GeorgeChiou/ESP32-CAM-MotorShield-V3.0-TANKGO/3DP STL TANKGO/截圖 2022-04-06 下午12.41.42.png

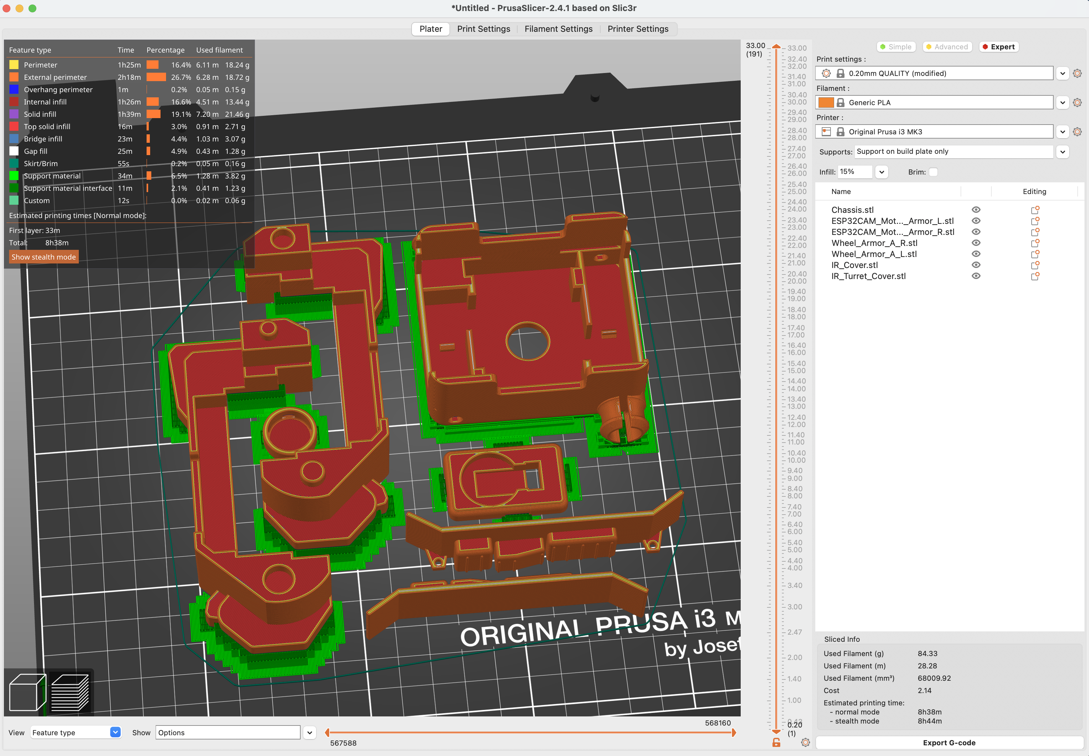
3DP STL TANKGO/截圖 2022-04-06 下午12.41.42.png
