GeorgeChiou/ESP32-CAM-MotorShield-V3.0-TANKGO/Pictures/IMG_5468.JPG

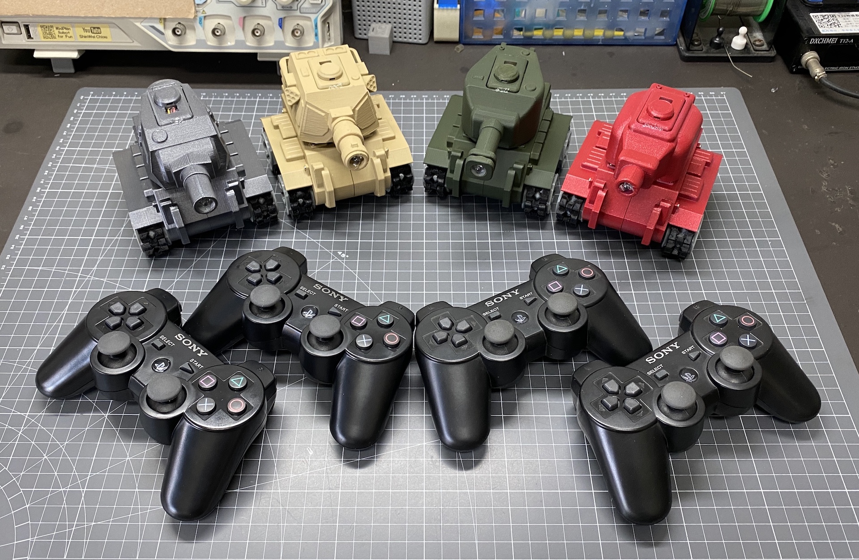
Pictures/IMG_5468.JPG
