GeorgeChiou/ESP32-CAM-MotorShield-V3.0-TANKGO/Program/Arduion IDE set.png

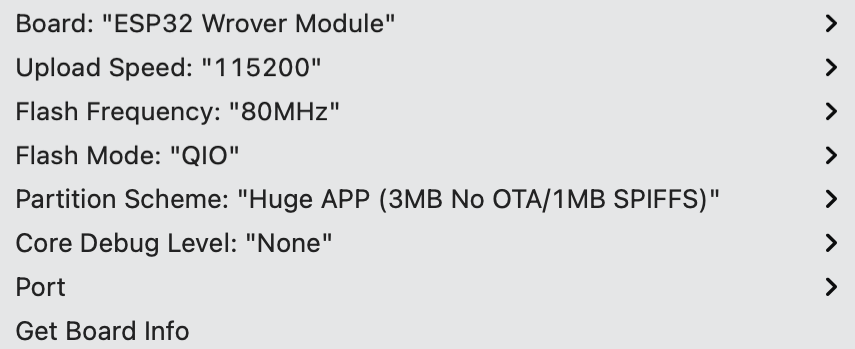
Program/Arduion IDE set.png
