GeorgeChiou/ESP32-CAM-MotorShield-V3.0-TANKGO/Assembly Instruction/ESP32-CAM Motor Shield V3.0  - Serial Pins for Upload Program.png

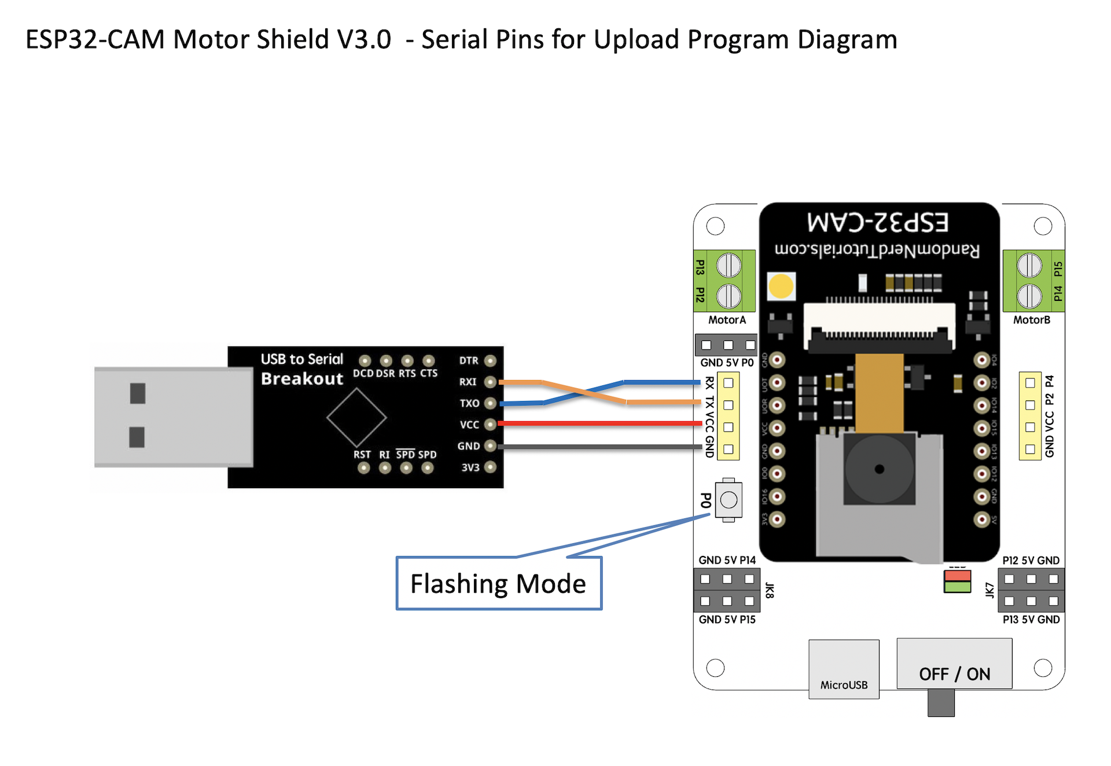
Program/ESP32-CAM Motor Shield V3.0 - Serial Pins for Upload Program.png
