GeorgeChiou/ESP32-CAM-MotorShield-V3.0-TANKGO/Assembly Instruction/ESP32-CAM Motor Shield V3.0  -  Battle Tower .png

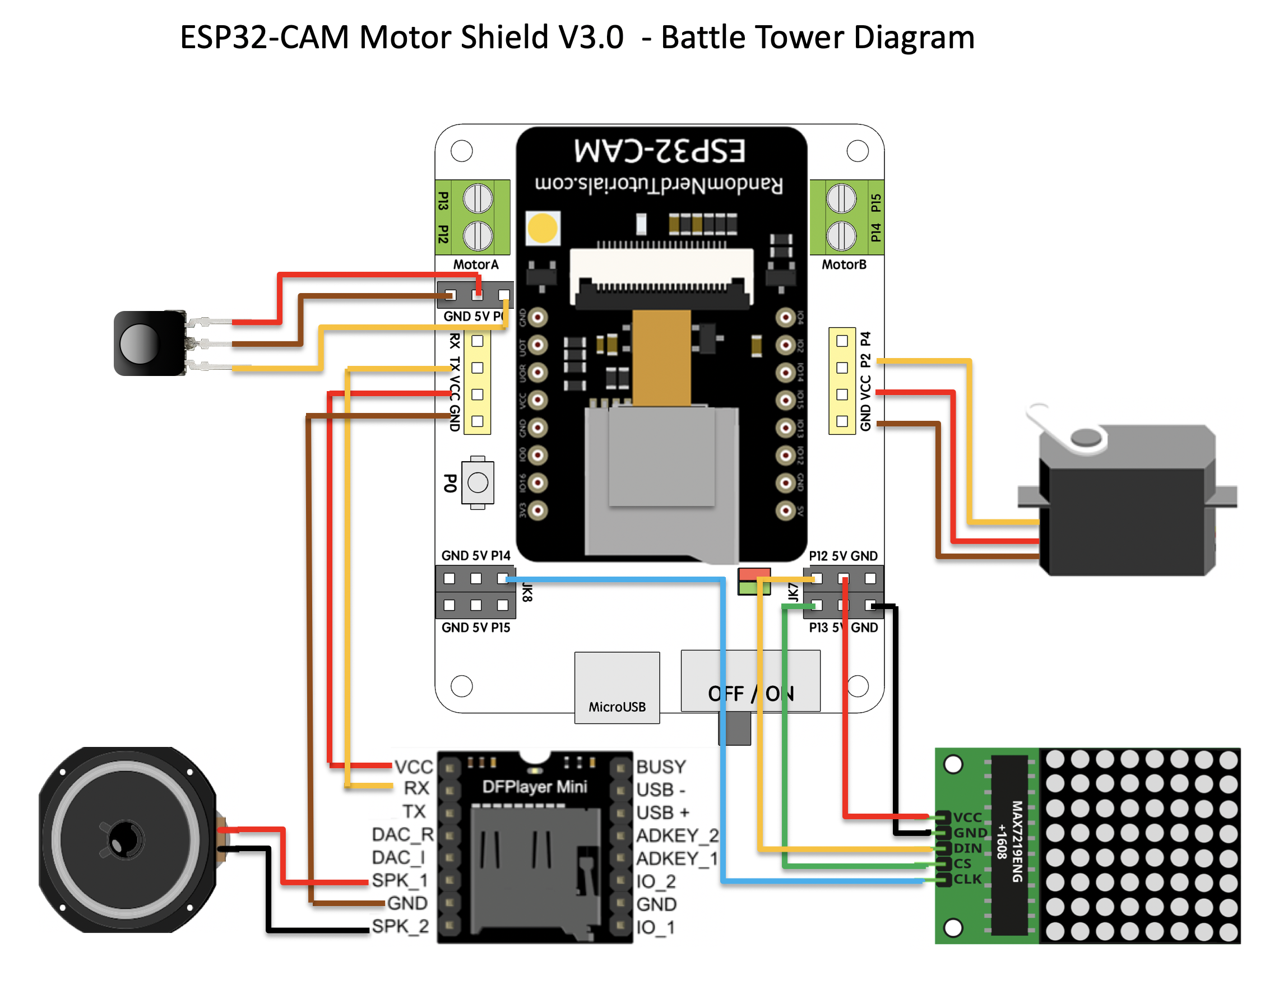
Program/ESP32CAM_MotorShieldV3_BattleTower_V100/ESP32-CAM Motor Shield V3.0 - Battle Tower .png
