GeorgeChiou/ESP32-CAM-MotorShield-V3.0-TANKGO/Program/ESP32CAM_MotorShieldV3_TANKGO_V100/ESP32-CAM Motor Shield V3.0  -  TANK GO.png

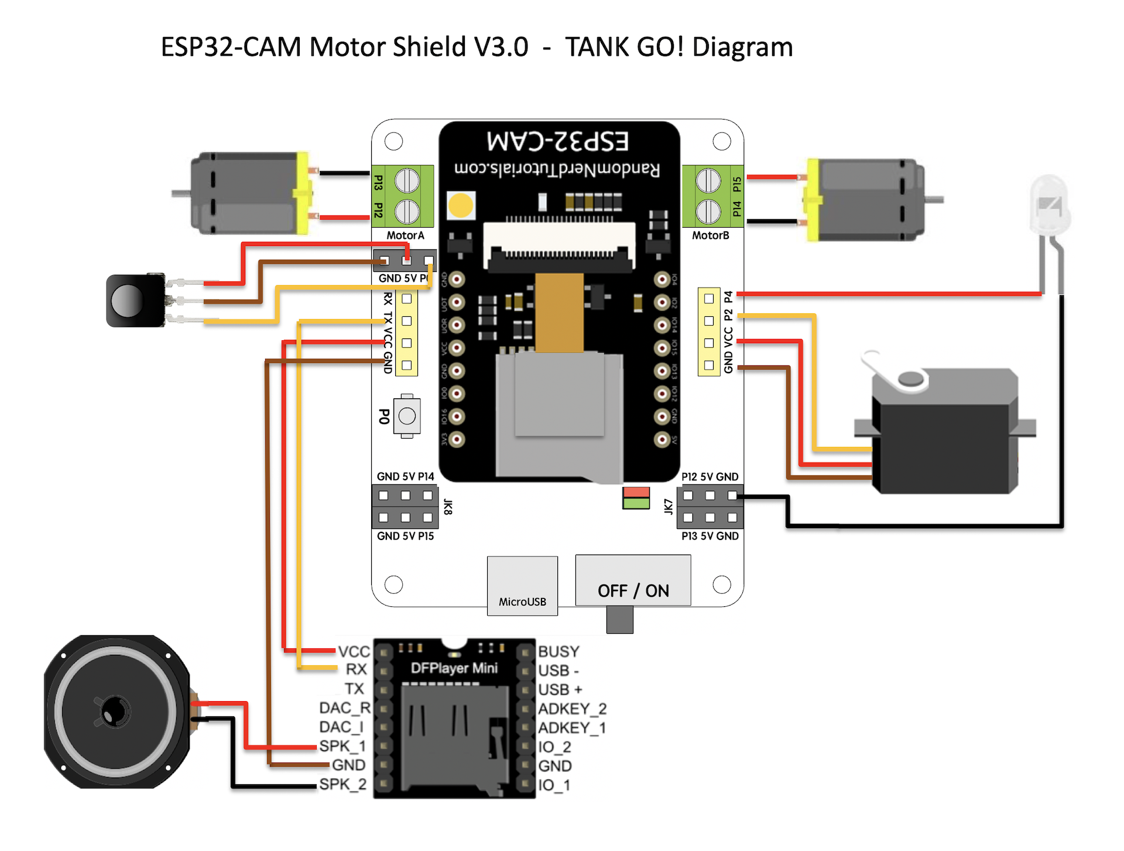
Program/ESP32CAM_MotorShieldV3_TANKGO_V100/ESP32-CAM Motor Shield V3.0 - TANK GO.png
