GeorgeChiou/ESP32-CAM-MotorShield-V3.0-TANKGO/3DP STL TANKGO/Turret_Sherman.stl

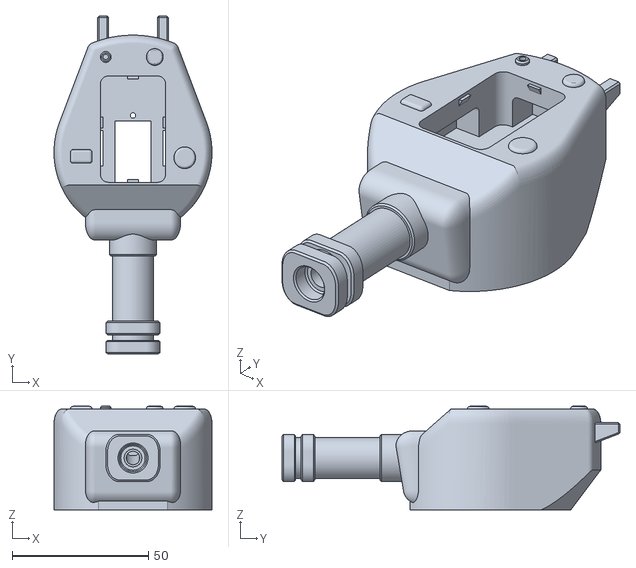
[picture p26: CAD file, 2022-06-05]
3DP STL TANKGO/Turret_Sherman.stl
58.0 x 124.0 x 38.0
