GeorgeChiou/ESP32-CAM-MotorShield-V3.0-TANKGO/3DP STL TANKGO/Wheel_Armor_S_2PCS.stl

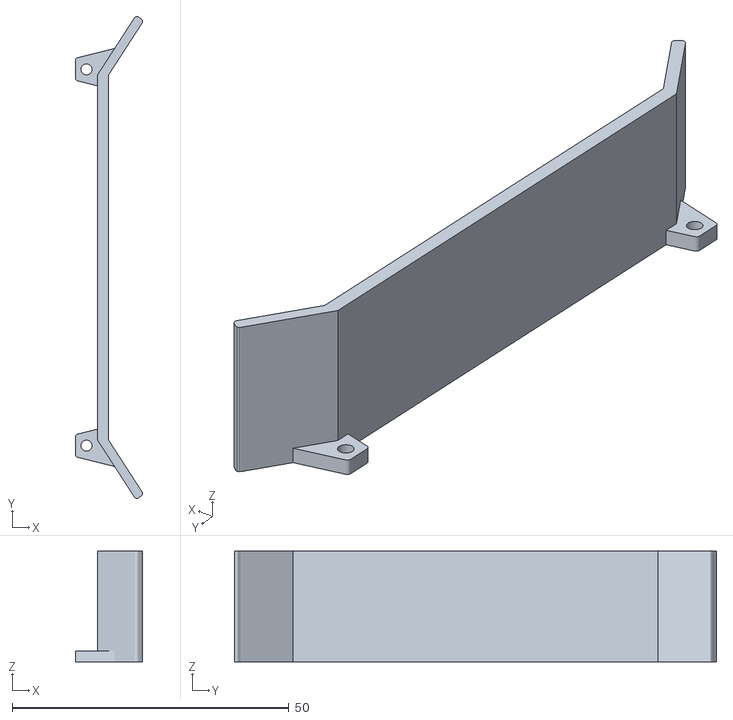
[picture p27: CAD file, 2022-06-05]
3DP STL TANKGO/Wheel_Armor_S_2PCS.stl
12.1 x 87.1 x 20.0
