GeorgeChiou/ESP32-CAM-MotorShield-V3.0-TANKGO/3DP STL TANKGO/Wheel_Armor_A_L.stl

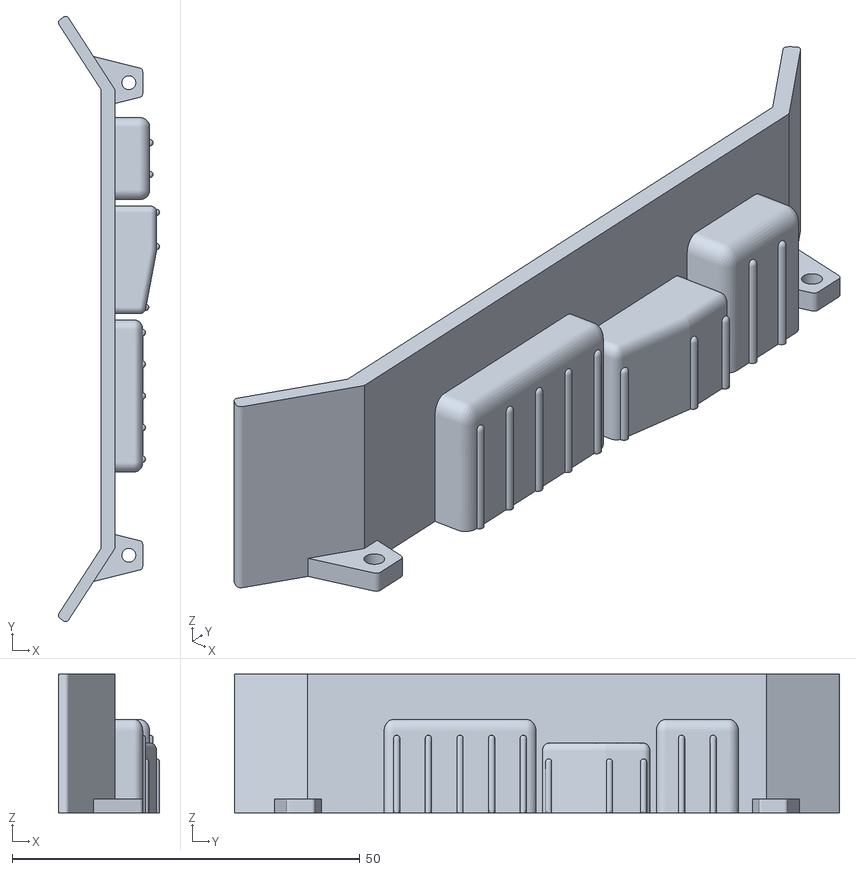
[picture p28: CAD file, 2022-06-05]
3DP STL TANKGO/Wheel_Armor_A_L.stl
14.6 x 87.1 x 20.0
