GeorgeChiou/ESP32-CAM-MotorShield-V3.0-TANKGO/3DP STL TANKGO/Wheel_Slave_2PCS.stl

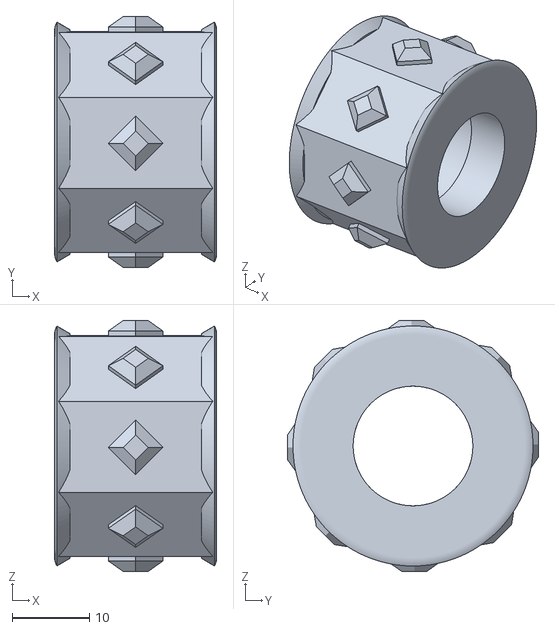
[picture p29: CAD file, 2022-06-05]
3DP STL TANKGO/Wheel_Slave_2PCS.stl
21.0 x 32.5 x 32.5
