GeorgeChiou/ESP32-CAM-MotorShield-V3.0-TANKGO/3DP STL TANKGO/Turret_TigerII.stl

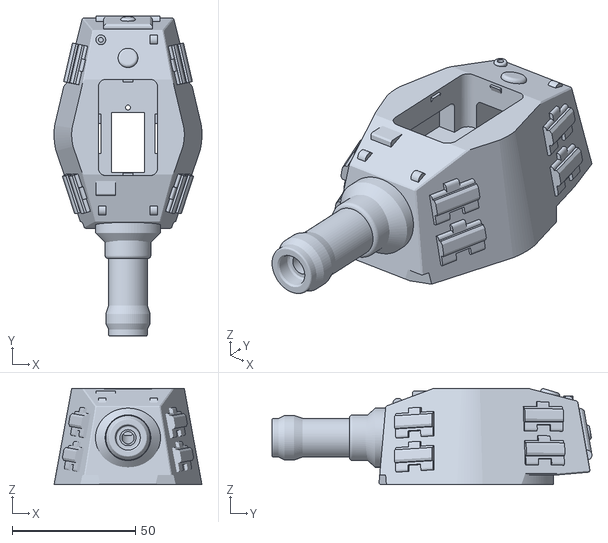
[picture p30: CAD file, 2022-06-05]
3DP STL TANKGO/Turret_TigerII.stl
59.9 x 129.6 x 39.0
