GeorgeChiou/ESP32-CAM-MotorShield-V3.0-TANKGO/3DP STL TANKGO/Turret_PanzerIV.stl

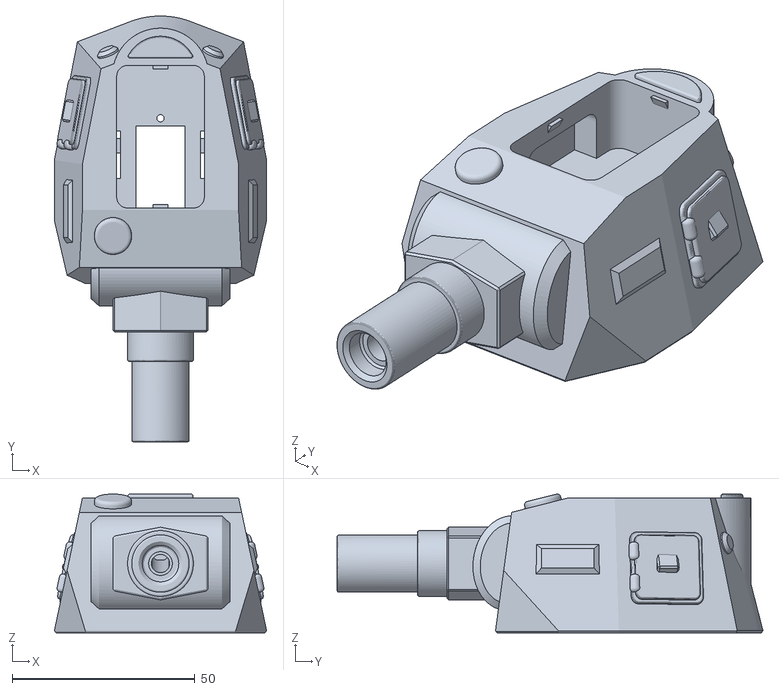
[picture p31: CAD file, 2022-06-05]
3DP STL TANKGO/Turret_PanzerIV.stl
58.1 x 116.6 x 38.0
