GeorgeChiou/ESP32-CAM-MotorShield-V3.0-TANKGO/3DP STL TANKGO/Wheel_Armor_T_2PCS.stl

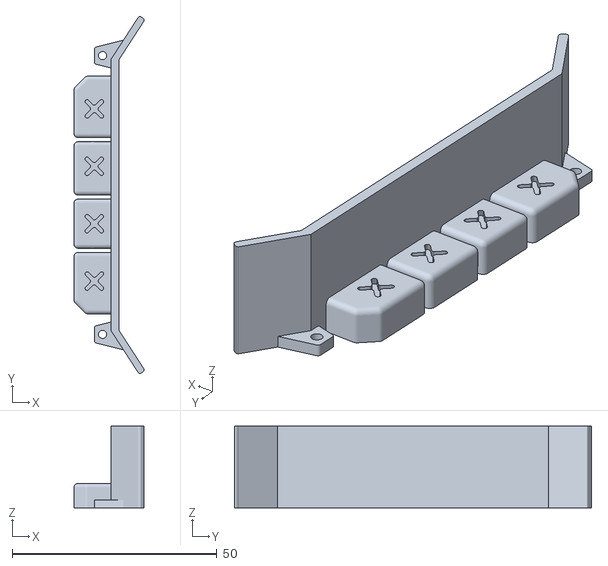
[picture p32: CAD file, 2022-06-05]
3DP STL TANKGO/Wheel_Armor_T_2PCS.stl
17.1 x 87.1 x 20.0
