GeorgeChiou/ESP32-CAM-MotorShield-V3.0-TANKGO/3DP STL TANKGO/Turret_X.stl

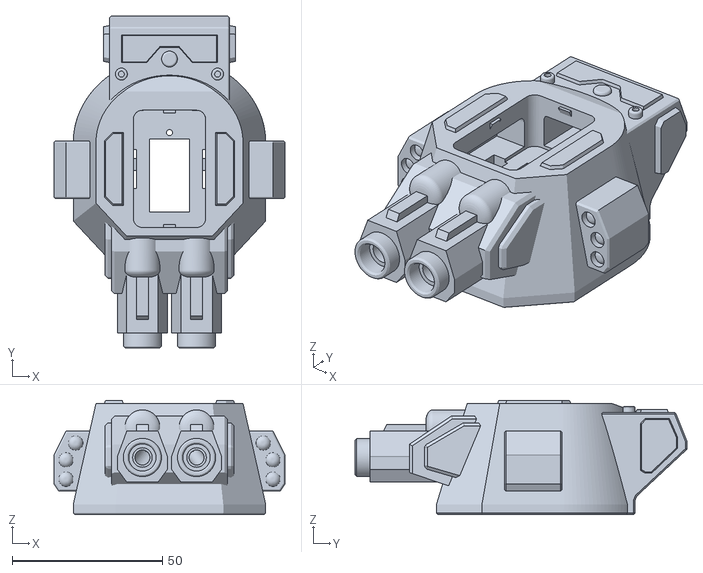
[picture p33: CAD file, 2022-06-05]
3DP STL TANKGO/Turret_X.stl
76.8 x 110.2 x 38.0
