GeorgeChiou/ESP32-CAM-MotorShield-V3.0-TANKGO/3DP STL TANKGO/Turret_Edelweiss.stl

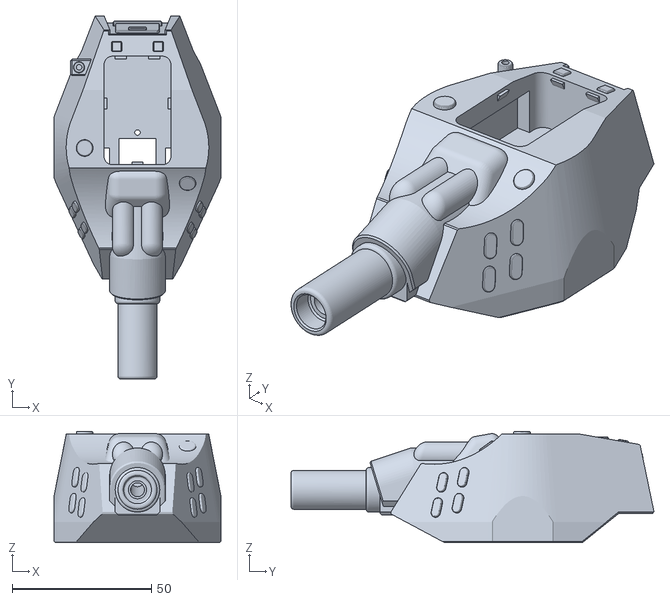
[picture p34: CAD file, 2022-06-05]
3DP STL TANKGO/Turret_Edelweiss.stl
60.0 x 130.4 x 40.0
