GeorgeChiou/ESP32-CAM-MotorShield-V3.0-TANKGO/3DP STL TANKGO/Track_32PCS.stl

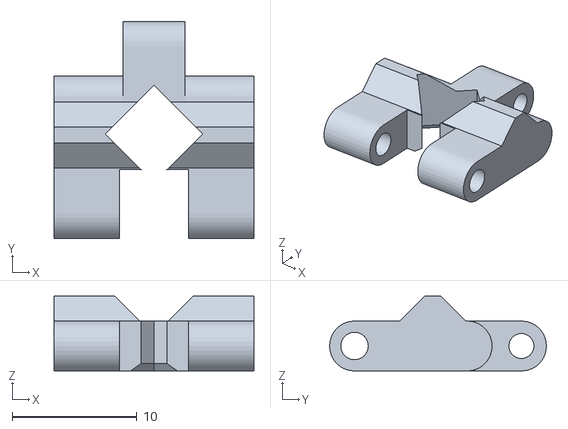
[picture p35: CAD file, 2022-06-05]
3DP STL TANKGO/Track_32PCS.stl
16.0 x 17.4 x 6.00
