GeorgeChiou/ESP32-CAM-MotorShield-V3.0-TANKGO/Assembly Instruction/DSC00377.JPG

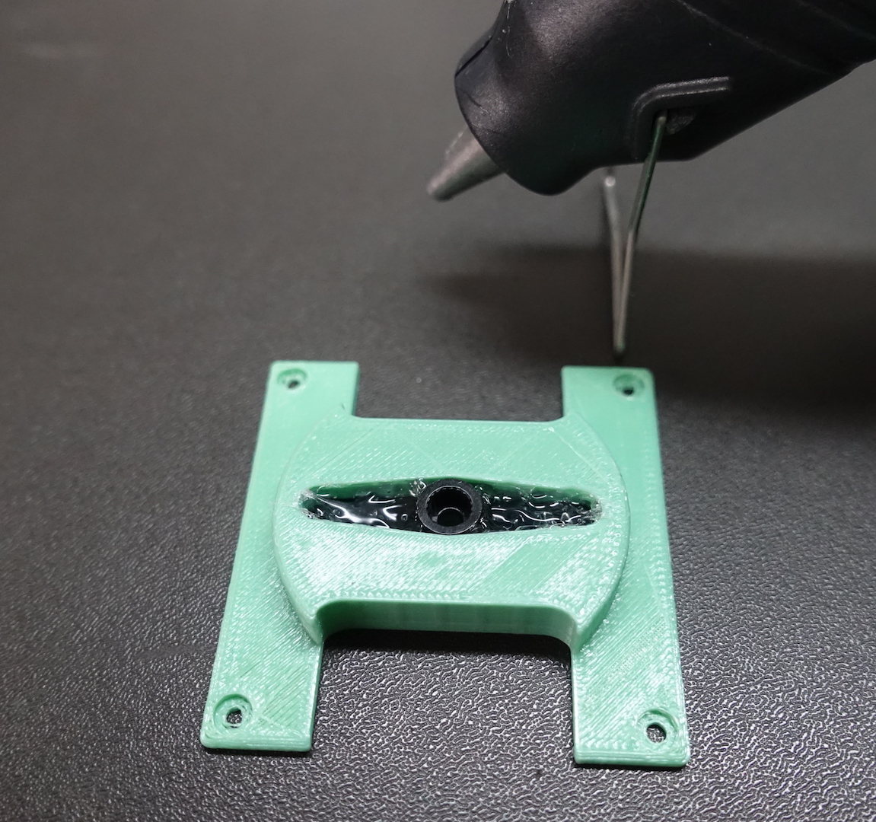
Assembly Instruction/DSC00377.JPG
