GeorgeChiou/ESP32-CAM-MotorShield-V3.0-TANKGO/Assembly Instruction/ESP32-CAM Motor Shield V3.0  -  TANK GO Motor.png

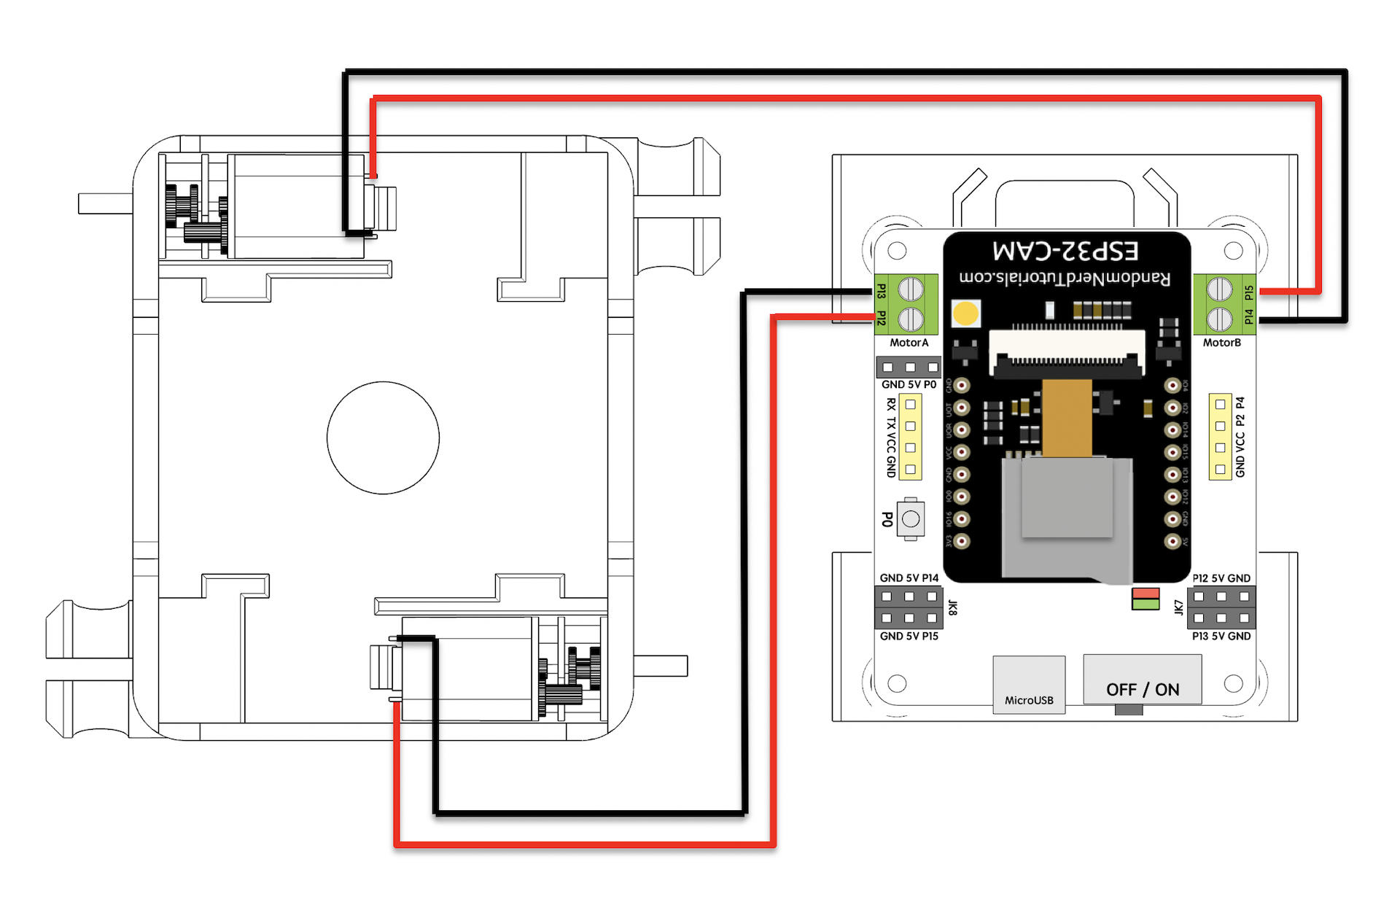
Assembly Instruction/ESP32-CAM Motor Shield V3.0 - TANK GO Motor.png
