GeorgeChiou/ESP32-CAM-MotorShield-V3.0-TANKGO/Assembly Instruction/TANK_GO_2.png

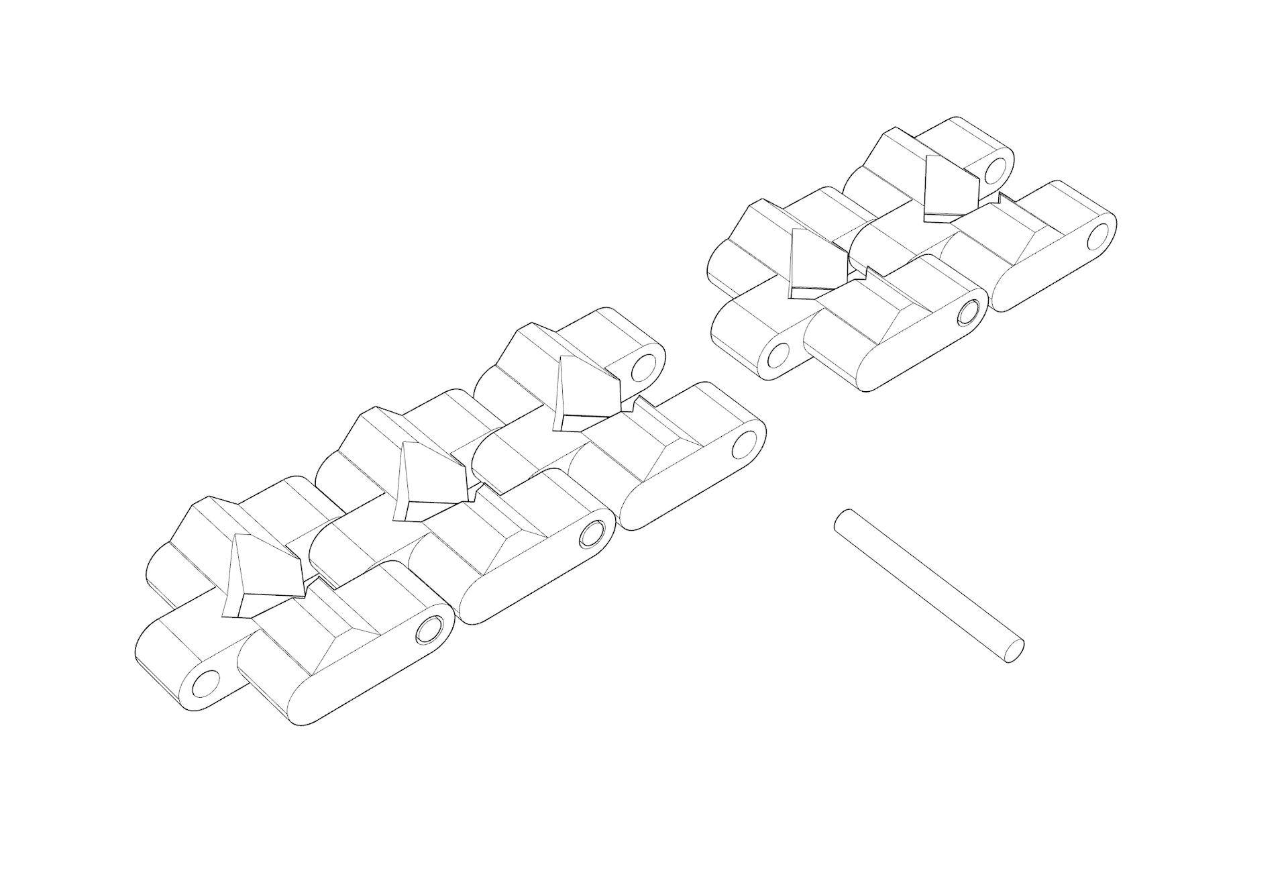
Assembly Instruction/TANK_GO_2.png
